Joel-Neuhaus-Khatami/XT-Keyboard-Project/pcb_files/xt_pcb/xt_pcb.kicad_sch

## KiCad design pcb_files/xt_pcb/xt_pcb.kicad_sch (2025-05-02)

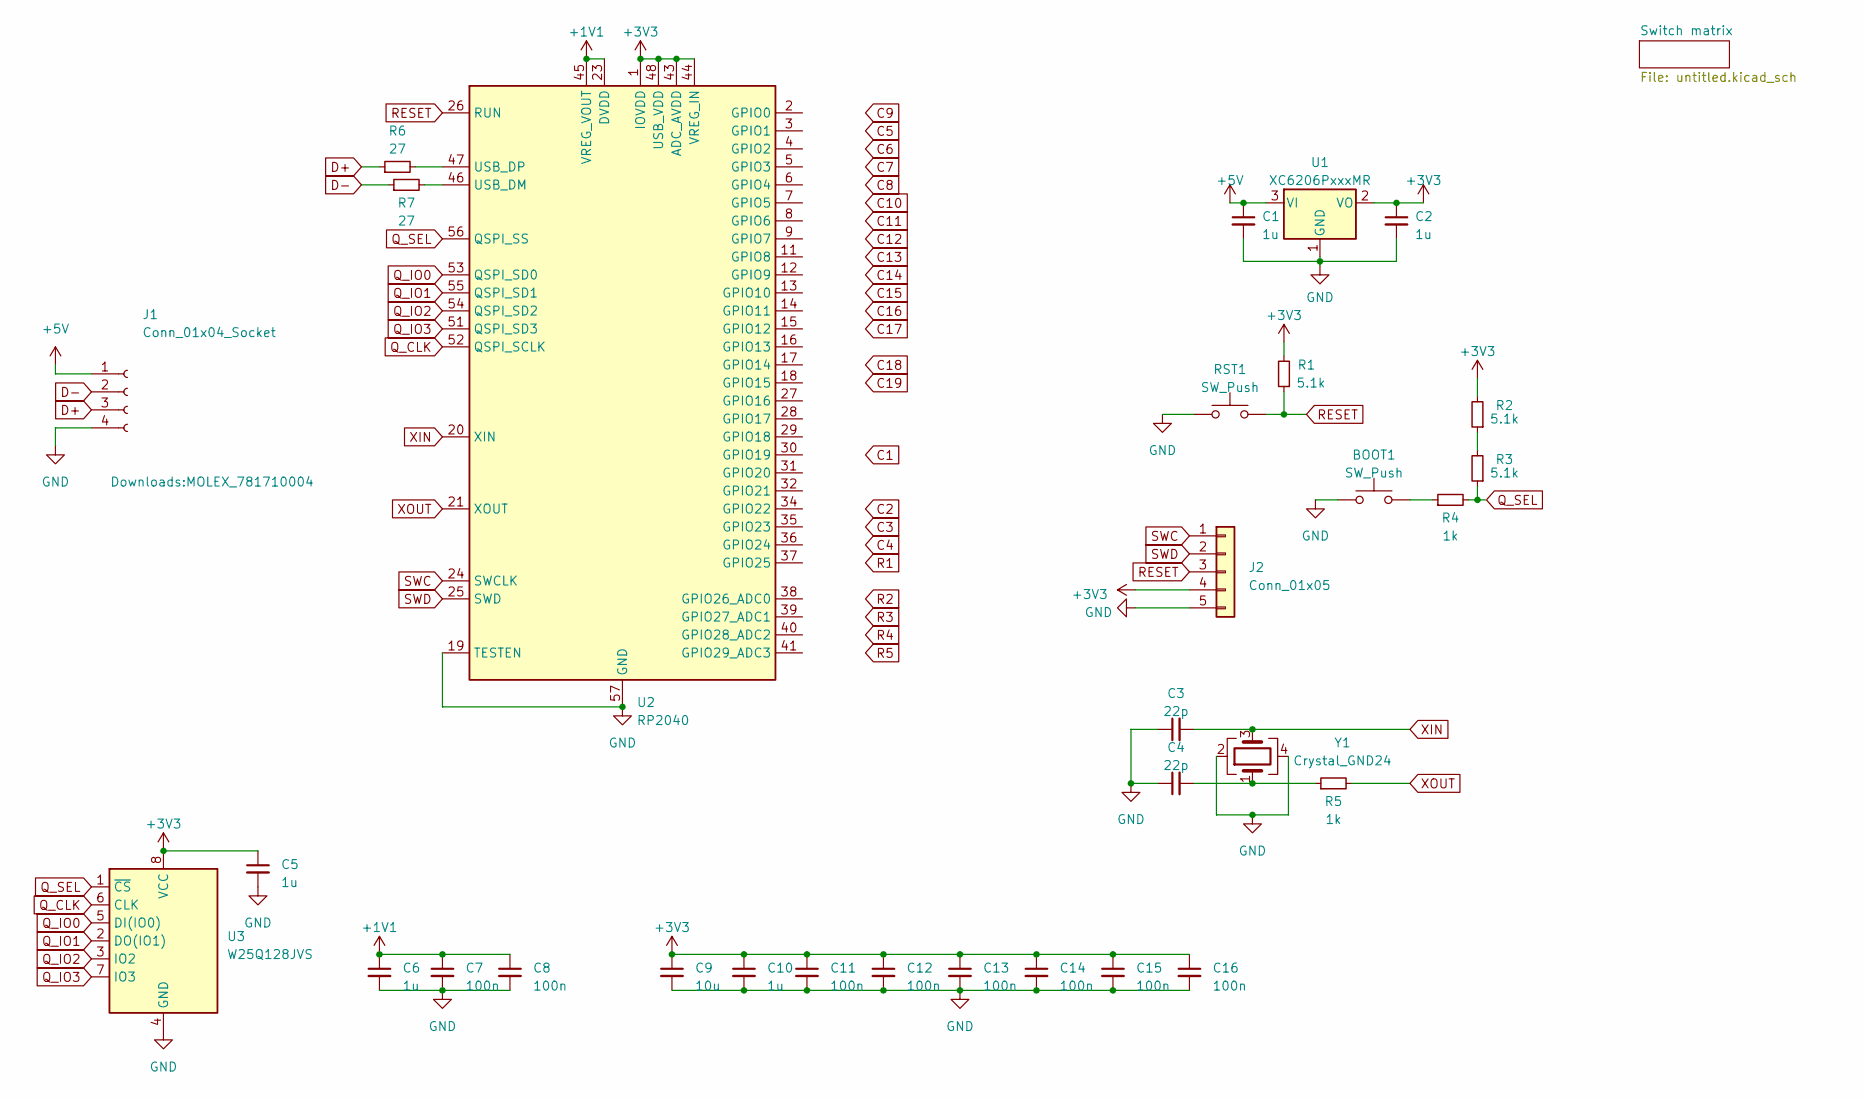
[picture p9: schematic xt_pcb.kicad_sch]

Parts:
BOOT1: SW_Push; SW_SPST_TL3342
C1, C2, C5, C6, C10: 1u; C_0402_1005Metric
C3, C4: 22p; C_0402_1005Metric
C7, C8, C11, C12, C13, C14, C15, C16: 100n; C_0402_1005Metric
C9: 10u; C_0603_1608Metric
J1: Conn_01x04_Socket; MOLEX_781710004
J2: Conn_01x05; PinHeader_1x05_P2.54mm_Vertical
R1, R2, R3: 5.1k; R_0402_1005Metric
R4, R5: 1k; R_0402_1005Metric
R6, R7: 27; R_0402_1005Metric
RST1: SW_Push; SW_SPST_TL3342
U1: XC6206PxxxMR; SOT-23-3
U2: RP2040; QFN-56-1EP_7x7mm_P0.4mm_EP3.2x3.2mm
U3: W25Q128JVS; SOIC-8_5.23x5.23mm_P1.27mm
Y1: Crystal_GND24; Crystal_SMD_3225-4Pin_3.2x2.5mm

Connections:
+1V1: C6.1, C7.1, C8.1, U2.23 (DVDD), U2.45 (VREG_VOUT), U2.50 (DVDD)
+3V3: C2.1, C5.1, C9.1, C10.1, C11.1, C12.1, C13.1, C14.1, C15.1, C16.1, J2.4, R1.2, R2.2, U1.2 (VO), U2.1 (IOVDD), U2.10 (IOVDD), U2.22 (IOVDD), U2.33 (IOVDD), U2.42 (IOVDD), U2.43 (ADC_AVDD), U2.44 (VREG_IN), U2.48 (USB_VDD), U2.49 (IOVDD), U3.8 (VCC)
+5V: C1.1, J1.1, U1.3 (VI)
D+: J1.3, R6.1
D-: J1.2, R7.1
GND: BOOT1.1, C1.2, C2.2, C3.1, C4.1, C5.2, C6.2, C7.2, C8.2, C9.2, C10.2, C11.2, C12.2, C13.2, C14.2, C15.2, C16.2, J1.4, J2.5, RST1.1, U1.1 (GND), U2.19 (TESTEN), U2.57 (GND), U3.4 (GND), Y1.2, Y1.4
unnamed: BOOT1.2, R4.1
unnamed: C4.2, R5.1, Y1.1
unnamed: R2.1, R3.2
unnamed: R6.2, U2.47 (USB_DP)
unnamed: R7.2, U2.46 (USB_DM)
Q_CLK: U2.52 (QSPI_SCLK), U3.6 (CLK)
Q_IO0: U2.53 (QSPI_SD0), U3.5 (DI(IO0))
Q_IO1: U2.55 (QSPI_SD1), U3.2 (DO(IO1))
Q_IO2: U2.54 (QSPI_SD2), U3.3 (IO2)
Q_IO3: U2.51 (QSPI_SD3), U3.7 (IO3)
Q_SEL: R3.1, R4.2, U2.56 (QSPI_SS), U3.1 (~CS)
RESET: J2.3, R1.1, RST1.2, U2.26 (RUN)
SWC: J2.1, U2.24 (SWCLK)
SWD: J2.2, U2.25 (SWD)
XIN: C3.2, U2.20 (XIN), Y1.3
XOUT: R5.2, U2.21 (XOUT)
